worxbend/macropad-nyxilab/docs/images/joystick/side.png

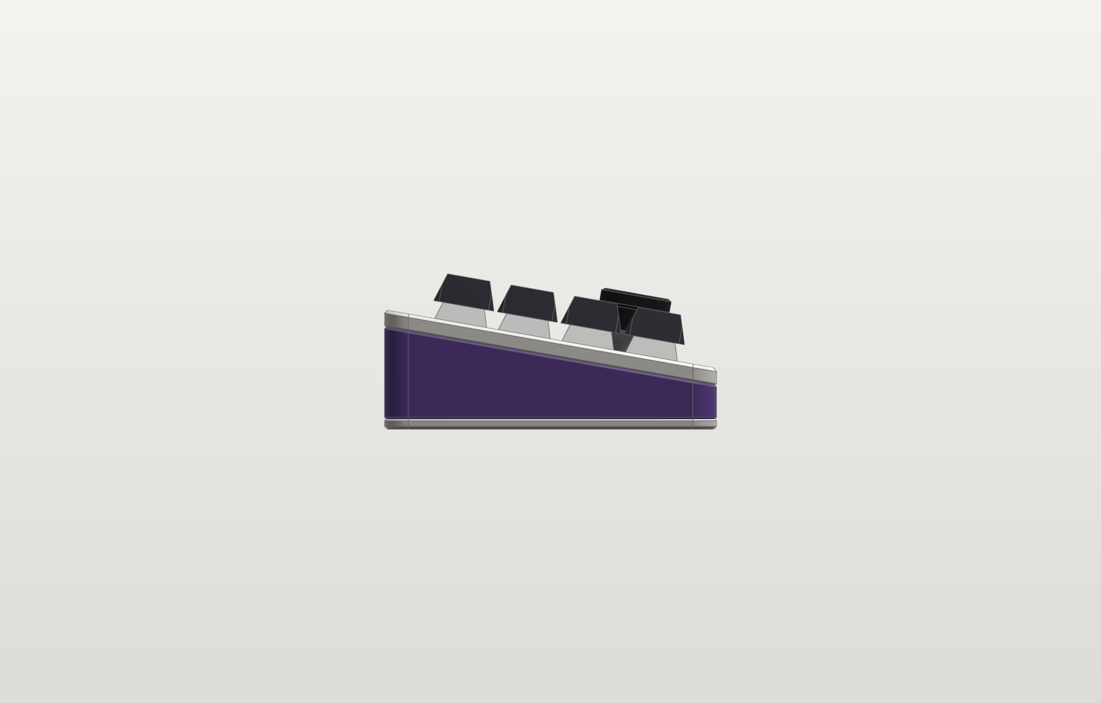
docs/images/joystick/side.png
