worxbend/macropad-nyxilab/docs/images/joystick/usb_detail.png

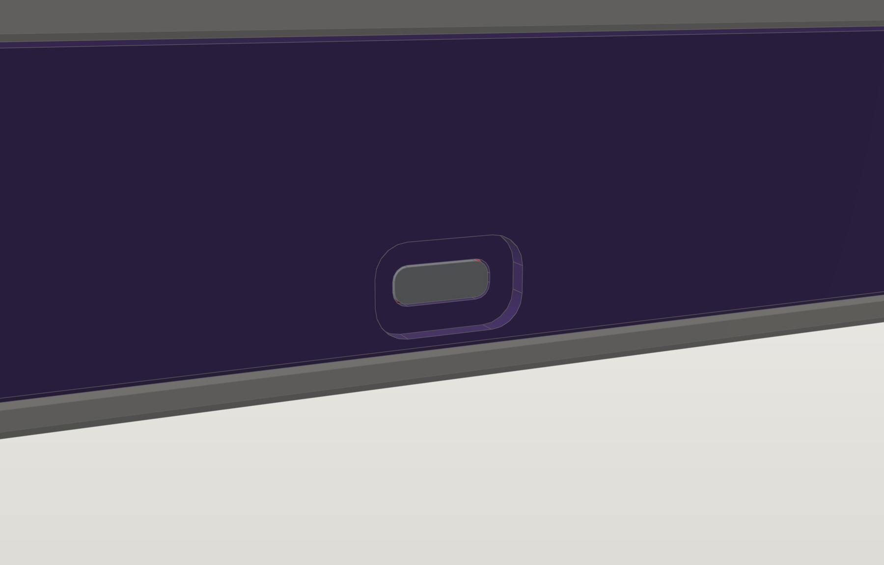
docs/images/joystick/usb_detail.png
