worxbend/macropad-nyxilab/docs/images/rotary/case_only.png

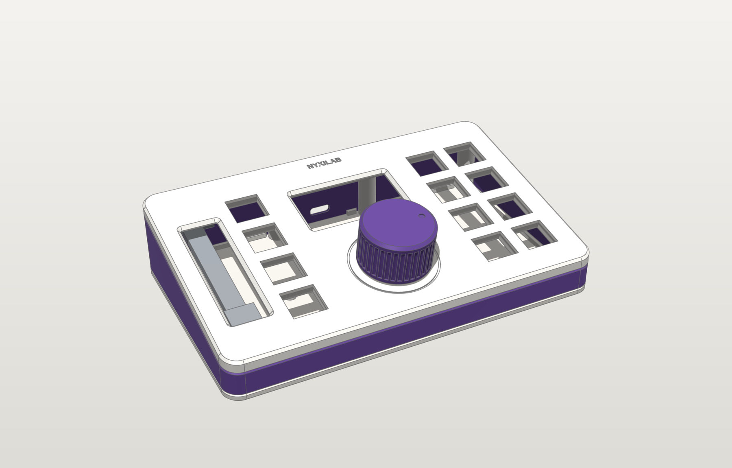
docs/images/rotary/case_only.png
