worxbend/macropad-nyxilab/rotary/cad/exports/step/frame.step

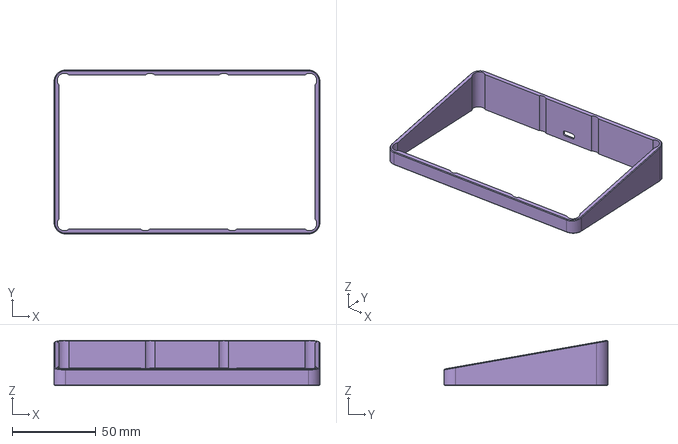
[picture p38: CAD file, 2026-09-28]
rotary/cad/exports/step/frame.step
158.9 x 98.0 x 27.1 mm
