worxbend/macropad-nyxilab/joystick/cad/exports/3mf/fit-tests/fit_joystick.3mf

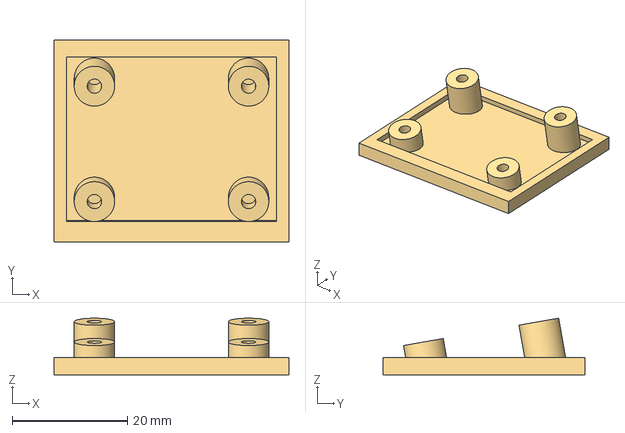
[picture p39: CAD file, 2026-09-28]
joystick/cad/exports/3mf/fit-tests/fit_joystick.3mf
40.7 x 35.0 x 9.81 mm
