worxbend/macropad-nyxilab/joystick/cad/exports/step/base.step

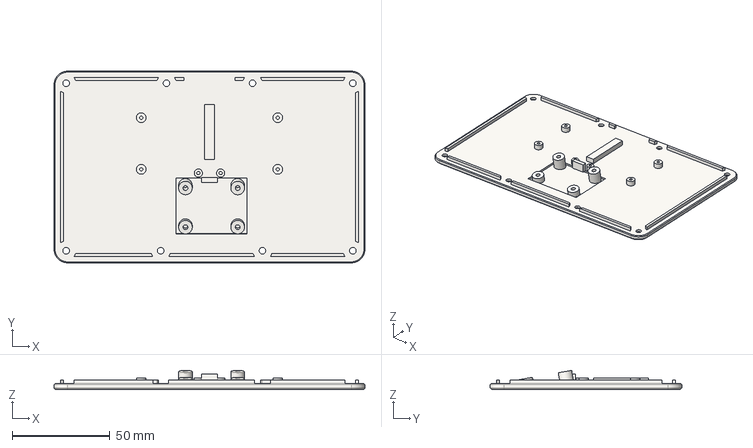
[picture p40: CAD file, 2026-09-28]
joystick/cad/exports/step/base.step
158.9 x 98.0 x 9.81 mm
