worxbend/macropad-nyxilab/rotary/cad/exports/step/knob.step

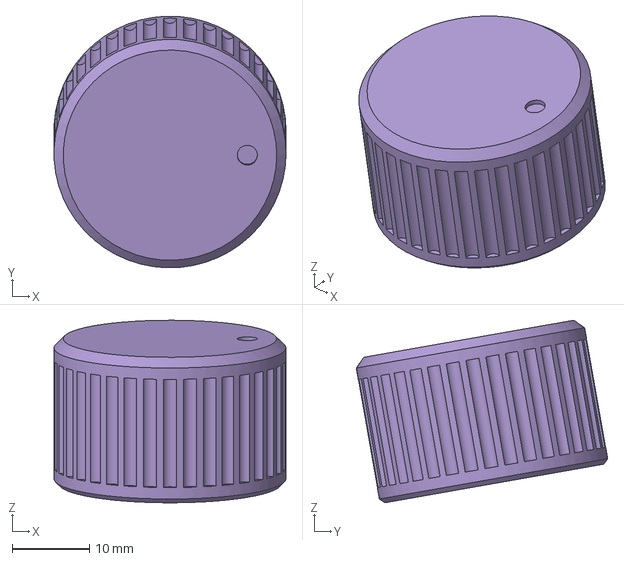
[picture p41: CAD file, 2026-09-28]
rotary/cad/exports/step/knob.step
30.0 x 32.5 x 23.6 mm
