worxbend/macropad-nyxilab/rotary/cad/exports/step/top_plate.step

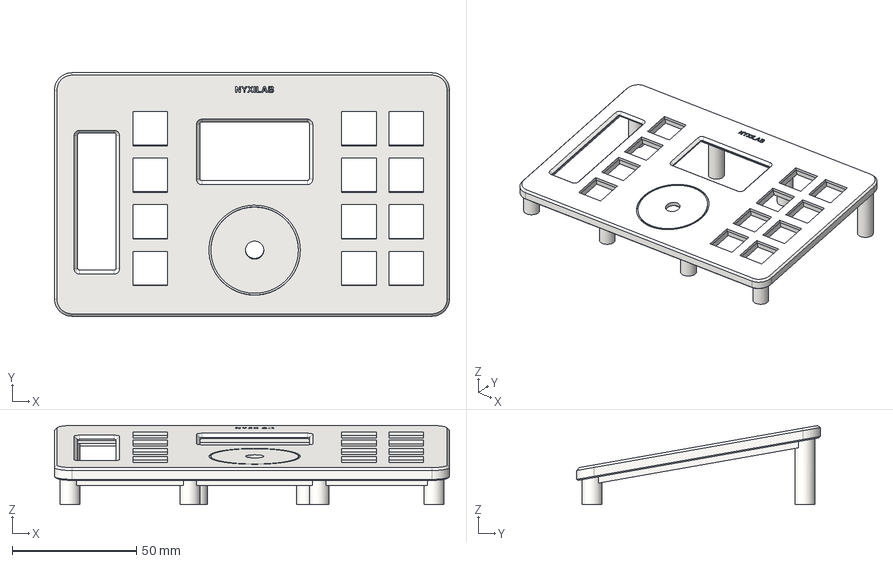
[picture p42: CAD file, 2026-09-28]
rotary/cad/exports/step/top_plate.step
158.9 x 98.0 x 31.8 mm
