worxbend/macropad-nyxilab/rotary/firmware/src/presets.h

// Knob presets that FN + KNOB cycles through, defined in keymap.cpp.
#pragma once
#include "core/keymap.h"

namespace mp {
extern const EncoderDef ENC_PRESETS[];
extern const uint8_t NUM_ENC_PRESETS;
}  // namespace mp
